xnvi/iot_led/doc/pic/220.jpg

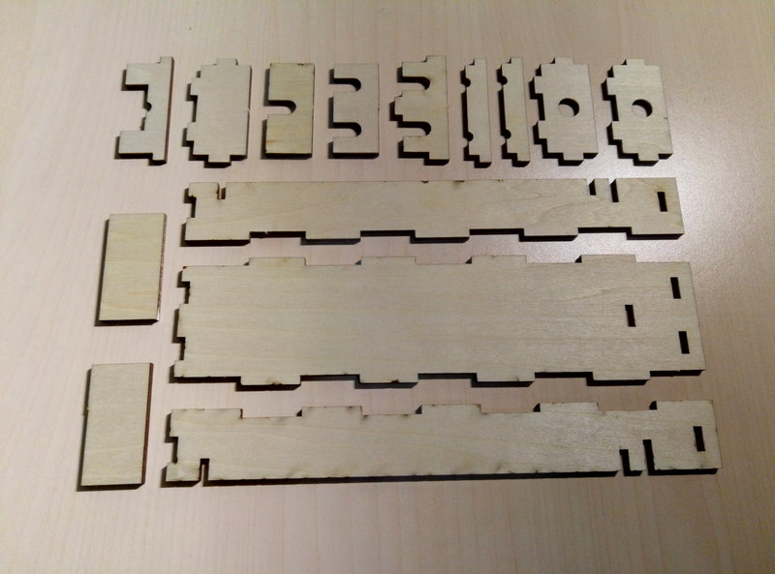
doc/pic/220.jpg
