xnvi/iot_led/doc/pic/260.jpg

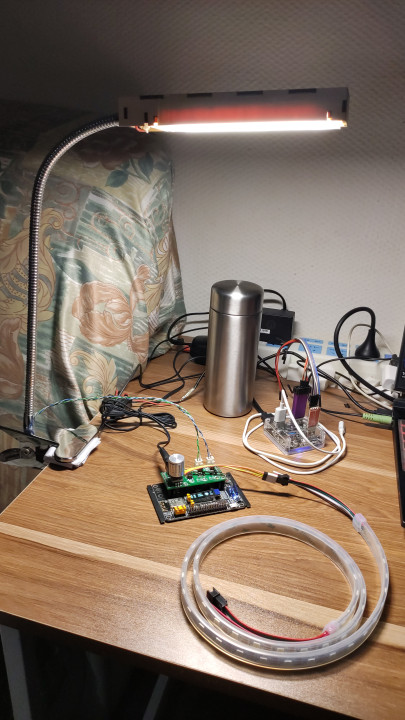
doc/pic/260.jpg
