xnvi/iot_led/doc/原理图及PCB/PCB预览_底面.png

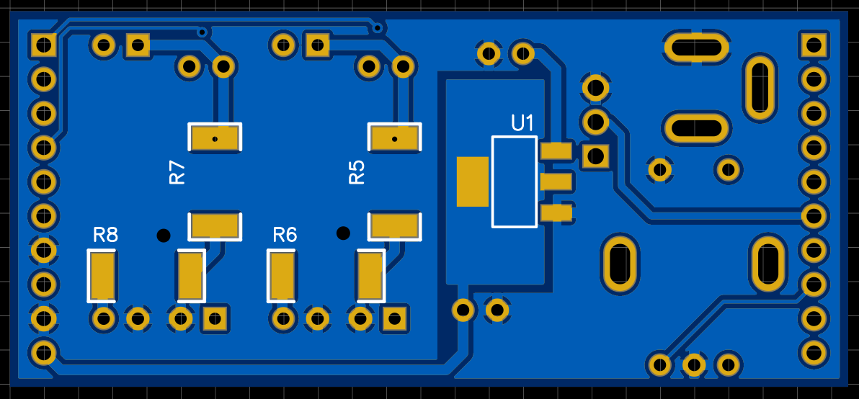
doc/原理图及PCB/PCB预览_底面.png
