xnvi/iot_led/user_code/encoder.h

#ifndef _ENCODER_H
#define _ENCODER_H

// EncoderKeyRet 返回编码器按键状态值
#define ENCODER_KEY_NULL 0x00
#define ENCODER_KEY_RELEASE 0x01
#define ENCODER_KEY_PRESS 0x02

void EncoderInit(void);
void EncoderScan(void);
char ReadEncoder(void);
unsigned char ReadEncoderKey(void);

#endif
