xnvi/iot_led/qcloud-iot-sdk-tencent-at-based/usr_logic/data_template_usr_logic.c

/*
 * Tencent is pleased to support the open source community by making IoT Hub available.
 * Copyright (C) 2019 THL A29 Limited, a Tencent company. All rights reserved.

 * Licensed under the MIT License (the "License"); you may not use this file except in
 * compliance with the License. You may obtain a copy of the License at
 * http://opensource.org/licenses/MIT

 * Unless required by applicable law or agreed to in writing, software distributed under the License is
 * distributed on an "AS IS" basis, WITHOUT WARRANTIES OR CONDITIONS OF ANY KIND,
 * either express or implied. See the License for the specific language governing permissions and
 * limitations under the License.
 *
 */
#include "qcloud_iot_api_export.h"
#include "lite-utils.h"
#include "at_client.h"
#include "string.h"
#include "data_config.c"

#include "user_task.h"


static bool sg_control_msg_arrived = false;
static char sg_data_report_buffer[AT_CMD_MAX_LEN];
static size_t sg_data_report_buffersize = sizeof(sg_data_report_buffer) / sizeof(sg_data_report_buffer[0]);


#ifdef EVENT_POST_ENABLED
#include "events_config.c"
#ifdef	EVENT_TIMESTAMP_USED
static void update_events_timestamp(sEvent *pEvents, int count)
{
	int i;
	
	for(i = 0; i < count; i++){
        if (NULL == (&pEvents[i])) { 
	        Log_e("null event pointer"); 
	        return; 
        }
		pEvents[i].timestamp = HAL_GetTimeSeconds();
	}
}
#endif 

static void event_post_cb(char *msg, void *context)
{
	Log_d("eventReply:%s", msg);
	IOT_Event_clearFlag(context, FLAG_EVENT0|FLAG_EVENT1|FLAG_EVENT2);
}

#endif

#ifdef ACTION_ENABLED
#include "action_config.c"

// action : regist action and set the action handle callback, add your aciton logic here
static void OnActionCallback(void *pClient, const char *pClientToken, DeviceAction *pAction) 
{	
	int i;
	sReplyPara replyPara;

	//do something base on input, just print as an sample
	DeviceProperty *pActionInput = pAction->pInput;
	for (i = 0; i < pAction->input_num; i++) {		
		if (JSTRING == pActionInput[i].type) {
			Log_d("Input:[%s], data:[%s]",  pActionInput[i].key, pActionInput[i].data);
			HAL_Free(pActionInput[i].data);
		} else {
			if(JINT32 == pActionInput[i].type) {
				Log_d("Input:[%s], data:[%d]",  pActionInput[i].key, *((int*)pActionInput[i].data));
			} else if( JFLOAT == pActionInput[i].type) {
				Log_d("Input:[%s], data:[%f]",  pActionInput[i].key, *((float*)pActionInput[i].data));
			} else if( JUINT32 == pActionInput[i].type) {
				Log_d("Input:[%s], data:[%u]",  pActionInput[i].key, *((uint32_t*)pActionInput[i].data));
			}
		}
	}	

	// construct output 
	memset((char *)&replyPara, 0, sizeof(sReplyPara));
	replyPara.code = eDEAL_SUCCESS;
	replyPara.timeout_ms = QCLOUD_IOT_MQTT_COMMAND_TIMEOUT;						
	strcpy(replyPara.status_msg, "action execute success!"); //add the message about the action resault 
	
	
	DeviceProperty *pActionOutnput = pAction->pOutput;	
	(void)pActionOutnput; //elimate warning
	//TO DO: add your aciont logic here and set output properties which will be reported by action_reply
	
	
	IOT_ACTION_REPLY(pClient, pClientToken, sg_data_report_buffer, sg_data_report_buffersize, pAction, &replyPara); 	
}

static int _register_data_template_action(void *pTemplate_client)
{
	int i,rc;
	
    for (i = 0; i < TOTAL_ACTION_COUNTS; i++) {
	    rc = IOT_Template_Register_Action(pTemplate_client, &g_actions[i], OnActionCallback);
	    if (rc != QCLOUD_RET_SUCCESS) {
	        rc = IOT_Template_Destroy(pTemplate_client);
	        Log_e("register device data template action failed, err: %d", rc);
	        return rc;
	    } else {
	        Log_i("data template action=%s registered.", g_actions[i].pActionId);
	    }
    }

	return QCLOUD_RET_SUCCESS;
}
#endif


static void OnControlMsgCallback(void *pClient, const char *pJsonValueBuffer, uint32_t valueLength, DeviceProperty *pProperty) 
{
    int i = 0;

    for (i = 0; i < TOTAL_PROPERTY_COUNT; i++) {		
        if (strcmp(sg_DataTemplate[i].data_property.key, pProperty->key) == 0) {
            sg_DataTemplate[i].state = eCHANGED;
            Log_i("Property=%s changed", pProperty->key);
            sg_control_msg_arrived = true;
            return;
        }
    }

    Log_e("Property=%s changed no match", pProperty->key);
}

/**
 * 注册数据模板属性
 */
static int _register_data_template_property(void *ptemplate_client)
{
	int i,rc;
	
    for (i = 0; i < TOTAL_PROPERTY_COUNT; i++) {
	    rc = IOT_Template_Register_Property(ptemplate_client, &sg_DataTemplate[i].data_property, OnControlMsgCallback);
	    if (rc != QCLOUD_RET_SUCCESS) {
	        rc = IOT_Template_Destroy(ptemplate_client);
	        Log_e("register device data template property failed, err: %d", rc);
	        return rc;
	    } else {
	        Log_i("data template property=%s registered.", sg_DataTemplate[i].data_property.key);
	    }
    }

	return QCLOUD_RET_SUCCESS;
}

static void OnReportReplyCallback(void *pClient, Method method, ReplyAck replyAck, const char *pJsonDocument, void *pUserdata) {
	Log_i("recv report_reply(ack=%d): %s", replyAck,pJsonDocument);
}


/*用户需要实现的下行数据的业务逻辑,待用户实现*/
static void deal_down_stream_user_logic(void *pClient, ProductDataDefine * pData)
{
	// Log_d("someting about your own product logic wait to be done");

	set_brightness(pData->m_brightness);
	set_color_temp(pData->m_color_temp);
	power_switch(pData->m_power_switch);
	set_colorful_mode(pData->m_colorful_mode, pData->m_default_color_mode,
	                  (pData->m_red << 16) + (pData->m_green << 8) + (pData->m_blue));
}

/*用户需要实现的上行数据的业务逻辑,此处仅供示例*/
static int deal_up_stream_user_logic(void *pClient, DeviceProperty *pReportDataList[], int *pCount)
{
	int i, j;
	
	//check local property state
	//_refresh_local_property. if property changed, set sg_DataTemplate[i].state = eCHANGED;
	
    for (i = 0, j = 0; i < TOTAL_PROPERTY_COUNT; i++) {       
        if(eCHANGED == sg_DataTemplate[i].state) {
            pReportDataList[j++] = &(sg_DataTemplate[i].data_property);
			sg_DataTemplate[i].state = eNOCHANGE;
        }
    }
	*pCount = j;

	return (*pCount > 0)?QCLOUD_RET_SUCCESS:QCLOUD_ERR_FAILURE;
}

static eAtResault net_prepare(void)
{
	eAtResault Ret;
	DeviceInfo sDevInfo;
	at_client_t pclient = at_client_get();	

	memset((char *)&sDevInfo, '\0', sizeof(DeviceInfo));
	Ret = (eAtResault)HAL_GetDevInfo(&sDevInfo);
	if(QCLOUD_RET_SUCCESS != Ret){
		Log_e("Get device info err");
		return QCLOUD_ERR_FAILURE;
	}
	
	if(QCLOUD_RET_SUCCESS != module_init(eMODULE_ESP8266)) 
	{
		Log_e("module init failed");
		goto exit;
	}
	else
	{
		Log_d("module init success");	
	}

	//wait at parse thread run
	while(AT_STATUS_INITIALIZED != pclient->status)
	{	
		HAL_SleepMs(1000);
	}
	
	Log_d("Start shakehands with module...");
	Ret = module_handshake(CMD_TIMEOUT_MS);
	if(QCLOUD_RET_SUCCESS != Ret)
	{
		Log_e("module connect fail,Ret:%d", Ret);
		goto exit;
	}
	else
	{
		Log_d("module connect success");
	}
	
	Ret = iot_device_info_init(sDevInfo.product_id, sDevInfo.device_name, sDevInfo.devSerc);
	if(QCLOUD_RET_SUCCESS != Ret)
	{
		Log_e("dev info init fail,Ret:%d", Ret);
		goto exit;
	}

	Ret = module_info_set(iot_device_info_get(), ePSK_TLS);
	if(QCLOUD_RET_SUCCESS != Ret)
	{
		Log_e("module info set fail,Ret:%d", Ret);
	}

exit:

	return Ret;
}

static void eventPostCheck(void *client)
{
#ifdef EVENT_POST_ENABLED	
	int rc;
	int i;
	uint32_t eflag;
	sEvent *pEventList[EVENT_COUNTS];
	uint8_t event_count;
		
	//事件上报
	IOT_Event_setFlag(client, FLAG_EVENT0|FLAG_EVENT1|FLAG_EVENT2);
	eflag = IOT_Event_getFlag(client);
	if((EVENT_COUNTS > 0 )&& (eflag > 0))
	{	
		event_count = 0;
		for(i = 0; i < EVENT_COUNTS; i++)
		{
		
			if((eflag&(1<<i))&ALL_EVENTS_MASK)
			{
				 pEventList[event_count++] = &(g_events[i]);				 
				 IOT_Event_clearFlag(client, 1<<i);
#ifdef	EVENT_TIMESTAMP_USED				 
				 update_events_timestamp(&g_events[i], 1);
#endif
			}			
		}	

		rc = IOT_Post_Event(client, sg_data_report_buffer, sg_data_report_buffersize, \
											event_count, pEventList, event_post_cb);
		if(rc < 0)
		{
			Log_e("events post failed: %d", rc);
		}
	}
#endif

}

/*用户需要实现设备信息获取,此处示例实现*/
static int _get_sys_info(void *handle, char *pJsonDoc, size_t sizeOfBuffer)
{
	/*平台处理字段，必选字段至少有一个*/
    DeviceProperty plat_info[] = {
     	{.key = "module_hardinfo", .type = TYPE_TEMPLATE_STRING, .data = "ESP8266"},
     	{.key = "module_softinfo", .type = TYPE_TEMPLATE_STRING, .data = "V1.0"},
     	{.key = "fw_ver", 		   .type = TYPE_TEMPLATE_STRING, .data = QCLOUD_IOT_AT_SDK_VERSION},
     	// {.key = "imei", 		   .type = TYPE_TEMPLATE_STRING, .data = "11-22-33-44"},
     	// {.key = "lat", 			   .type = TYPE_TEMPLATE_STRING, .data = "22.546015"},
     	// {.key = "lon", 			   .type = TYPE_TEMPLATE_STRING, .data = "113.941125"},
        {NULL, NULL, JINT32}  //结束
	};
		
	/*自定义附加信息*/
	DeviceProperty self_info[] = {
        {.key = "append_info", .type = TYPE_TEMPLATE_STRING, .data = "your self define ifno"},
        {NULL, NULL, JINT32}  //结束
	};

	return IOT_Template_JSON_ConstructSysInfo(handle, pJsonDoc, sizeOfBuffer, plat_info, self_info); 	
}


void data_template_demo_task(void *arg)
{
	eAtResault Ret;
	int rc;
	int ReportCont;
	void *client = NULL;
	at_client_t pclient = at_client_get();	
	DeviceProperty *pReportDataList[TOTAL_PROPERTY_COUNT];

	Log_d("data_template_demo_task Entry...");
	do  
	{
		Ret = net_prepare();
		if(QCLOUD_RET_SUCCESS != Ret)
		{
			Log_e("net prepare fail,Ret:%d", Ret);
			break;
		}

		/*
		 *注意：module_register_network 联网需要根据所选模组适配修改实现
		*/
		Ret = module_register_network(eMODULE_ESP8266);
		if(QCLOUD_RET_SUCCESS != Ret)
		{			
			Log_e("network connect fail,Ret:%d", Ret);
			break;
		}

		
		MQTTInitParams init_params = DEFAULT_MQTTINIT_PARAMS;
		Ret = module_mqtt_conn(init_params);
		if(QCLOUD_RET_SUCCESS != Ret)
		{
			Log_e("module mqtt conn fail,Ret:%d", Ret);
			break;
		}
		else
		{
			Log_d("module mqtt conn success");
		}

		
		if(!IOT_MQTT_IsConnected())
		{
			Log_e("mqtt connect fail");
			break;
		}

		Ret = (eAtResault)IOT_Template_Construct(&client);
		if(QCLOUD_RET_SUCCESS != Ret)
		{
			Log_e("data template construct fail,Ret:%d", Ret);
			break;
		}
		else
		{
			Log_d("data template construct success");
		}

		//init data template
		_init_data_template();

				
		//register data template propertys here
		rc = _register_data_template_property(client);
		if (rc == QCLOUD_RET_SUCCESS) 
		{
			Log_i("Register data template propertys Success");
		} 
		else 
		{
			Log_e("Register data template propertys Failed: %d", rc);
			break;
		}

#ifdef ACTION_ENABLED
		//register data template actions
		rc = _register_data_template_action(client);
		if (rc == QCLOUD_RET_SUCCESS) {
			Log_i("Register data template actions Success");
		} else {
			Log_e("Register data template actions Failed: %d", rc);
			break;
		}
#endif
			
		//上报设备信息,平台根据这个信息提供产品层面的数据分析,譬如位置服务等
		rc = _get_sys_info(client, sg_data_report_buffer, sg_data_report_buffersize);
		if(QCLOUD_RET_SUCCESS == rc)
		{
			rc = IOT_Template_Report_SysInfo_Sync(client, sg_data_report_buffer, sg_data_report_buffersize, QCLOUD_IOT_MQTT_COMMAND_TIMEOUT);	
			if (rc != QCLOUD_RET_SUCCESS) 
			{
				Log_e("Report system info fail, err: %d", rc);
				break;
			}
		}
		else
		{
			Log_e("Get system info fail, err: %d", rc);
			break;
		}

		//获取离线期间数据
		rc = IOT_Template_GetStatus_sync(client, QCLOUD_IOT_MQTT_COMMAND_TIMEOUT);
		if (rc != QCLOUD_RET_SUCCESS) 
		{
			Log_e("Get data status fail, err: %d", rc);
			break;
		}
		else
		{
			Log_d("Get data status success");
		}


		while(1)
		{
			HAL_SleepMs(1000);
			IOT_Template_Yield(client, 2000);
			
			/*服务端下行消息，业务处理逻辑1入口*/
			if (sg_control_msg_arrived) {	
				
				deal_down_stream_user_logic(client, &sg_ProductData);				
				//业务逻辑处理完后需要通知服务端control msg 已收到，请服务端删除control msg，否则服务端会保留control msg(通过Get status命令可以得到未删除的Control数据)
				sReplyPara replyPara;
				memset((char *)&replyPara, 0, sizeof(sReplyPara));
				replyPara.code = eDEAL_SUCCESS;
				replyPara.timeout_ms = QCLOUD_IOT_MQTT_COMMAND_TIMEOUT;						
				replyPara.status_msg[0] = '\0';			//可以通过 replyPara.status_msg 添加附加消息，一般在失败情况下才添加
				
				rc = IOT_Template_ControlReply(client, sg_data_report_buffer, sg_data_report_buffersize, &replyPara);
	            if (rc == QCLOUD_RET_SUCCESS) {
					Log_d("Contol msg reply success");
					sg_control_msg_arrived = false;   
	            } else {
	                Log_e("Contol msg reply failed, err: %d", rc);
					break;
	            }				
			}	

			/*设备上行消息,业务逻辑2入口*/								
			if(QCLOUD_RET_SUCCESS == deal_up_stream_user_logic(client, pReportDataList, &ReportCont)){
				
				rc = IOT_Template_JSON_ConstructReportArray(client, sg_data_report_buffer, sg_data_report_buffersize, ReportCont, pReportDataList);
				if (rc == QCLOUD_RET_SUCCESS) {
					rc = IOT_Template_Report(client, sg_data_report_buffer, sg_data_report_buffersize, 
												OnReportReplyCallback, NULL, QCLOUD_IOT_MQTT_COMMAND_TIMEOUT);
					if (rc == QCLOUD_RET_SUCCESS) {
						Log_d("data template reporte success");
					} else {
						Log_e("data template reporte failed, err: %d", rc);
						break;
					}
				} else {
					Log_e("construct reporte data failed, err: %d", rc);
					break;
				}
		
			}
			
			// TODO 暂时不需要上报事件，以后要用再开发
			// eventPostCheck(client);
		}				
	}while (0);
	
	hal_thread_destroy(NULL);
	Log_e("Task teminated,Something goes wrong!!!");
}

void data_template_sample(void)
{
	osThreadId demo_threadId;
	
#ifdef OS_USED
	// TODO 默认512，改大一点，实际测试需要3K，根据自己实际情况修改
	hal_thread_create(&demo_threadId, 3072, osPriorityNormal, data_template_demo_task, NULL);
	hal_thread_destroy(NULL);
#else
	#error os should be used just now
#endif
}

extern void start_user_task(void *arg);

void application_entry(void *arg)
{
	start_user_task(NULL);
	data_template_sample();
}
