xnvi/iot_led/user_code/ascii12.h

#ifndef _ASCII12_H
#define _ASCII12_H

//��λ��ǰȡģ
/*
const unsigned char ASCII12 [1140] = {
0x00,0x00,0x00,0x00,0x00,0x00,0x00,0x00,0x00,0x00,0x00,0x00,
0x00,0x00,0x7F,0x00,0x00,0x00,0x00,0x00,0xA0,0x00,0x00,0x00,
0x00,0x60,0x00,0x60,0x00,0x00,0x00,0x00,0x00,0x00,0x00,0x00,
0x11,0x7F,0x11,0x7F,0x11,0x00,0x00,0xE0,0x00,0xE0,0x00,0x00,
0x18,0x24,0x7F,0x22,0x11,0x00,0x80,0x40,0xE0,0x40,0x80,0x00,
0x30,0x49,0x36,0x19,0x60,0x00,0x60,0x80,0xC0,0x20,0xC0,0x00,
0x3B,0x44,0x46,0x39,0x02,0x00,0xC0,0x20,0x20,0xC0,0x20,0x00,
0x00,0x00,0x60,0x00,0x00,0x00,0x00,0x00,0x00,0x00,0x00,0x00,
0x00,0x0F,0x30,0x40,0x00,0x00,0x00,0x00,0xC0,0x20,0x00,0x00,
0x00,0x40,0x30,0x0F,0x00,0x00,0x00,0x20,0xC0,0x00,0x00,0x00,
0x11,0x0A,0x3F,0x0A,0x11,0x00,0x00,0x00,0x80,0x00,0x00,0x00,
0x04,0x04,0x1F,0x04,0x04,0x00,0x00,0x00,0x00,0x00,0x00,0x00,
0x00,0x00,0x00,0x00,0x00,0x00,0x00,0xA0,0xC0,0x00,0x00,0x00,
0x04,0x04,0x04,0x04,0x04,0x00,0x00,0x00,0x00,0x00,0x00,0x00,
0x00,0x00,0x00,0x00,0x00,0x00,0x00,0x60,0x60,0x00,0x00,0x00,
0x00,0x01,0x06,0x18,0x60,0x00,0x60,0x80,0x00,0x00,0x00,0x00,
0x3F,0x41,0x42,0x44,0x3F,0x00,0xC0,0x20,0x20,0x20,0xC0,0x00,
0x00,0x20,0x7F,0x00,0x00,0x00,0x00,0x20,0xE0,0x20,0x00,0x00,
0x30,0x41,0x42,0x44,0x38,0x00,0xE0,0x20,0x20,0x20,0x20,0x00,
0x30,0x40,0x44,0x44,0x3B,0x00,0xC0,0x20,0x20,0x20,0xC0,0x00,
0x03,0x0C,0x30,0x7F,0x00,0x00,0x80,0x80,0x80,0xE0,0x80,0x00,
0x7C,0x44,0x44,0x44,0x43,0x00,0x40,0x20,0x20,0x20,0xC0,0x00,
0x3F,0x44,0x44,0x44,0x23,0x00,0xC0,0x20,0x20,0x20,0xC0,0x00,
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
0xfe,0x02,0x02,0x02,0xfc,0x00,0x07,0x04,0x04,0x04,0x03,0x00,
0xfe,0x22,0x22,0x22,0x02,0x00,0x07,0x04,0x04,0x04,0x04,0x00,
0xfe,0x22,0x22,0x22,0x02,0x00,0x07,0x00,0x00,0x00,0x00,0x00,
0xfc,0x02,0x42,0x42,0xcc,0x00,0x03,0x04,0x04,0x02,0x07,0x00,
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
};

#endif
