xnvi/iot_led/user_code/zh_cn12.h

/*
字库取模方式
目前用的 PCtoLCD2002
阴码 逆向（低位在前） 列行式

*/


#ifndef _ZH_CN12_H
#define _ZH_CN12_H

// #include "myinteger.h"
#include<stdint.h>

// 使用用户字库，或使用默认字库，默认字库为字频表前1024字，可覆盖大部分使用场景
#define USE_USER_FONT_TABLE 1
#define USE_DEFAULT_FONT_TABLE 0


typedef struct _FONT12_STRUCT
{
	uint8_t character[3];
	uint8_t reserve;
	uint8_t fontdata[24];
}font12_struct;


#if 0
// !!!! 二分查找要求所有汉字索引必须排序 !!!!
// const font12_struct font12_table[] = 
const font12_struct font12_table[] = 
{
	{"测", 0, {0x22,0x44,0xFE,0x02,0xFA,0x02,0xFE,0x00,0xFC,0x00,0xFF,0x00,0x04,0x02,0x09,0x04,0x03,0x04,0x09,0x00,0x01,0x08,0x0F,0x00},},
	{"试", 0, {0x11,0xF2,0x00,0x00,0x24,0xE4,0x24,0x04,0xFF,0x04,0x05,0x00,0x00,0x0F,0x04,0x00,0x04,0x07,0x02,0x00,0x03,0x04,0x0E,0x00},},
	{"文", 0, {0x04,0x04,0x1C,0x64,0x85,0x06,0x84,0x64,0x1C,0x04,0x04,0x00,0x08,0x08,0x04,0x04,0x02,0x01,0x02,0x04,0x04,0x08,0x08,0x00},},
	{"中", 0, {0x00,0xF8,0x88,0x88,0x88,0xFF,0x88,0x88,0x88,0xF8,0x00,0x00,0x00,0x01,0x00,0x00,0x00,0x0F,0x00,0x00,0x00,0x01,0x00,0x00},},
};
#endif


#if USE_USER_FONT_TABLE

const font12_struct font12_table[] = 
{
	{"亮", 0, {0x82,0x82,0xBA,0xAA,0xAA,0xAB,0xAA,0xAA,0xBA,0x82,0x82,0x00,0x09,0x08,0x06,0x02,0x02,0x02,0x02,0x06,0x08,0x08,0x0D,0x00},},
	{"度", 0, {0x00,0xFE,0x0A,0x8A,0xBE,0xAA,0xAB,0xAA,0xBE,0x8A,0x0A,0x00,0x08,0x07,0x00,0x08,0x09,0x0A,0x04,0x04,0x0A,0x09,0x08,0x00},},
	{"色", 0, {0x08,0xF4,0x92,0x93,0x92,0xF2,0x92,0x9A,0x96,0xF0,0x00,0x00,0x00,0x07,0x08,0x08,0x08,0x08,0x08,0x08,0x08,0x08,0x0E,0x00},},
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
	{"九", 0, {0x08,0x08,0x08,0xFF,0x08,0x08,0x08,0xF8,0x00,0x00,0x00,0x00,0x08,0x04,0x03,0x00,0x00,0x00,0x00,0x07,0x08,0x08,0x0E,0x00},},
	{"十", 0, {0x20,0x20,0x20,0x20,0x20,0xFF,0x20,0x20,0x20,0x20,0x20,0x00,0x00,0x00,0x00,0x00,0x00,0x0F,0x00,0x00,0x00,0x00,0x00,0x00},},
	{"，", 0, {0x00,0x00,0xC0,0xC0,0x00,0x00,0x00,0x00,0x00,0x00,0x00,0x00,0x00,0x00,0x02,0x01,0x00,0x00,0x00,0x00,0x00,0x00,0x00,0x00},},
	{"。", 0, {0x00,0x00,0xC0,0x20,0x20,0xC0,0x00,0x00,0x00,0x00,0x00,0x00,0x00,0x00,0x00,0x01,0x01,0x00,0x00,0x00,0x00,0x00,0x00,0x00},},
};

#endif // USE_USER_FONT_TABLE



#if USE_DEFAULT_FONT_TABLE

const font12_struct font12_table[] = 
{

};

#endif // USE_USER_FONT_TABLE

#endif // _ZH_CN12_H
