xnvi/iot_led/qcloud-iot-sdk-tencent-at-based/port/hal_os.c

/*
 * Tencent is pleased to support the open source community by making IoT Hub available.
 * Copyright (C) 2016 THL A29 Limited, a Tencent company. All rights reserved.

 * Licensed under the MIT License (the "License"); you may not use this file except in
 * compliance with the License. You may obtain a copy of the License at
 * http://opensource.org/licenses/MIT

 * Unless required by applicable law or agreed to in writing, software distributed under the License is
 * distributed on an "AS IS" basis, WITHOUT WARRANTIES OR CONDITIONS OF ANY KIND,
 * either express or implied. See the License for the specific language governing permissions and
 * limitations under the License.
 *
 */

#include <stdio.h>
#include <stdlib.h>
#include <stdarg.h>
#include <string.h>
#include "stm32g0xx_hal.h"		
#include "qcloud_iot_api_export.h"
#include "tos_k.h"
#include "user_config.h"

#ifdef  DEBUG_DEV_INFO_USED

/* 产品名称, 与云端同步设备状态时需要  */
static char sg_product_id[MAX_SIZE_OF_PRODUCT_ID + 1]	 = USER_PRODUCT_ID;
/* 设备名称, 与云端同步设备状态时需要 */
static char sg_device_name[MAX_SIZE_OF_DEVICE_NAME + 1]  = USER_DEVICE_NAME;

#ifdef DEV_DYN_REG_ENABLED
/* 产品密钥, 若使能动态注册功能，控制台生成，必填。若不使能，则不用赋值  */
static char sg_product_secret[MAX_SIZE_OF_PRODUCT_SECRET + 1]  = "YOUR_PRODUCT_SECRET";
#endif

#ifdef AUTH_MODE_CERT
/* 客户端证书文件名  非对称加密使用, TLS 证书认证方式*/
static char sg_device_cert_file_name[MAX_SIZE_OF_DEVICE_CERT_FILE_NAME + 1]      = "YOUR_DEVICE_NAME_cert.crt";
/* 客户端私钥文件名 非对称加密使用, TLS 证书认证方式*/
static char sg_device_privatekey_file_name[MAX_SIZE_OF_DEVICE_KEY_FILE_NAME + 1] = "YOUR_DEVICE_NAME_private.key";
#else
/* 设备密钥, TLS PSK认证方式*/
static char sg_device_secret[MAX_SIZE_OF_DEVICE_SERC + 1] = USER_DEVICE_SECRET;
#endif


#endif

void HAL_Printf(_IN_ const char *fmt, ...)
{
    va_list args;

    va_start(args, fmt);
    vprintf(fmt, args);
    va_end(args);

    fflush(stdout);
}

int HAL_Snprintf(_IN_ char *str, const int len, const char *fmt, ...)
{
    va_list args;
    int rc;

    va_start(args, fmt);
    rc = vsnprintf(str, len, fmt, args);
    va_end(args);

    return rc;
}

int HAL_Vsnprintf(_IN_ char *str, _IN_ const int len, _IN_ const char *format, va_list ap)
{
    return vsnprintf(str, len, format, ap);
}


void HAL_DelayUs(_IN_ uint32_t us)
{
    HAL_Delay(us);
}

uint32_t HAL_GetTimeMs(void)
{	
    return HAL_GetTick();
}

uint32_t HAL_GetTimeSeconds(void)
{	
    return HAL_GetTimeMs()/1000;
}


void HAL_DelayMs(_IN_ uint32_t ms)
{
   (void)HAL_Delay(ms);
}

#ifdef OS_USED

// 实际使用中AT SDK一共创建2个任务
#define AT_SDK_TASK_NUM 2
#define AT_SDK_TASK_NAME_LEN 16

char task_name_list[AT_SDK_TASK_NUM][AT_SDK_TASK_NAME_LEN];
k_task_t *task_list[AT_SDK_TASK_NUM];
	
void hal_thread_create(volatile void* threadId, uint16_t stackSize, int Priority, void (*fn)(void*), void* arg)
{
	int i = 0;
	k_err_t err;

	for(i=0; i<AT_SDK_TASK_NUM; i++)
	{
		if(task_list[i] == NULL)
		{
			break;
		}
	}

	sprintf(&task_name_list[i][0], "at_task_%d", i);

	err = tos_task_create_dyn((k_task_t **)threadId,
							  &task_name_list[i][0],
							  (k_task_entry_t)fn,
							  arg,
							  4,
							  stackSize,
							  0);
	if (err != K_ERR_NONE)
	{
		printf("hal_thread_create err, ret %d\n", err);
	}
	task_list[i] = (k_task_t *)threadId;
}

void hal_thread_destroy(void* threadId)
{
	k_err_t err;
	int i = 0;

	for(i=0; i<AT_SDK_TASK_NUM; i++)
	{
		if(task_list[i] == threadId)
		{
			task_list[i] = NULL;
			memset(&task_name_list[i][0], 0, AT_SDK_TASK_NAME_LEN);
			break;
		}
	}

	err = tos_task_destroy(threadId);
	if (err != K_ERR_NONE)
	{
		printf("hal_thread_destroy err, ret %d\n", err);
	}
}

void HAL_SleepMs(_IN_ uint32_t ms)
{
   (void)osDelay(ms);
}

void *HAL_Malloc(_IN_ uint32_t size)
{
	return tos_mmheap_alloc(size);
}

void HAL_Free(_IN_ void *ptr)
{
	tos_mmheap_free(ptr);
}


// 锁的数量请根据实际情况修改
#define LOCK_NUM 4
k_mutex_t lock_list[LOCK_NUM];
unsigned char lock_index[LOCK_NUM] = {0};

void *HAL_MutexCreate(void)
{
	k_err_t err;
	int i = 0;
	for(i=0; i<LOCK_NUM; i++)
	{
		if(lock_index[i] == 0)
		{
			lock_index[i] = 1;
			break;
		}
	}

	if(i >= LOCK_NUM)
	{
		return NULL;
	}
	
	err = tos_mutex_create(&lock_list[i]);
    return err == K_ERR_NONE ? &lock_list[i] : NULL;
}


void HAL_MutexDestroy(_IN_ void * mutex)
{
	int i = 0;
	for(i=0; i<LOCK_NUM; i++)
	{
		if(&lock_list[i] == mutex)
		{
			lock_index[i] = 0;
			break;
		}
	}

	tos_mutex_destroy((k_mutex_t *)mutex);
}

void HAL_MutexLock(_IN_ void * mutex)
{
	k_err_t ret;
	ret = tos_mutex_pend_timed((k_mutex_t *)mutex, TOS_TIME_FOREVER);
	if(ret)
	{
		HAL_Printf("HAL_MutexLock err, err:%d\n\r",ret);
	}
}

void HAL_MutexUnlock(_IN_ void * mutex)
{
	k_err_t ret;
	ret = tos_mutex_post((k_mutex_t *)mutex);
	if(ret)
	{
		HAL_Printf("HAL_MutexUnlock err, err:%d\n\r",ret);
	}	
}
#else
void hal_thread_create(void** threadId, void (*fn)(void*), void* arg)
{

}

void HAL_SleepMs(_IN_ uint32_t ms)
{
	(void)HAL_Delay(ms);
}

void *HAL_Malloc(_IN_ uint32_t size)
{
	return malloc(size);
}

void HAL_Free(_IN_ void *ptr)
{
   free(ptr);
}

void *HAL_MutexCreate(void)
{
	return (void *)1;
}


void HAL_MutexDestroy(_IN_ void* mutex)
{
	return;
}

void HAL_MutexLock(_IN_ void* mutex)
{
	return;
}

void HAL_MutexUnlock(_IN_ void* mutex)
{
	return;
}

#endif

int HAL_SetDevInfo(void *pdevInfo)
{
	int ret = QCLOUD_RET_SUCCESS;;
	DeviceInfo *devInfo = (DeviceInfo *)pdevInfo;
	

	if(NULL == pdevInfo){
		return QCLOUD_ERR_FAILURE;
	}
	
#ifdef DEBUG_DEV_INFO_USED
	memset(sg_product_id, '\0', MAX_SIZE_OF_PRODUCT_ID);	
	memset(sg_device_name, '\0', MAX_SIZE_OF_DEVICE_NAME);
	
	strncpy(sg_product_id, devInfo->product_id, MAX_SIZE_OF_PRODUCT_ID);
	strncpy(sg_device_name, devInfo->device_name, MAX_SIZE_OF_DEVICE_NAME);
	
#ifdef DEV_DYN_REG_ENABLED
	memset(sg_product_secret, '\0', MAX_SIZE_OF_PRODUCT_SECRET);
	strncpy(sg_product_secret, devInfo->product_secret, MAX_SIZE_OF_PRODUCT_KEY);
#endif
	
#ifdef 	AUTH_MODE_CERT
	memset(sg_device_cert_file_name, '\0', MAX_SIZE_OF_DEVICE_CERT_FILE_NAME);
	memset(sg_device_privatekey_file_name, '\0', MAX_SIZE_OF_DEVICE_KEY_FILE_NAME);
	
	strncpy(sg_device_cert_file_name, devInfo->devCertFileName, MAX_SIZE_OF_DEVICE_CERT_FILE_NAME);
	strncpy(sg_device_privatekey_file_name, devInfo->devPrivateKeyFileName, MAX_SIZE_OF_DEVICE_KEY_FILE_NAME);
#else
	memset(sg_device_secret, '\0', MAX_SIZE_OF_DEVICE_SERC);
	strncpy(sg_device_secret, devInfo->devSerc, MAX_SIZE_OF_DEVICE_SERC);
#endif
		
#else
	 Log_e("HAL_SetDevInfo is not implement");
	 (void)devInfo; //eliminate compile warning

	 return QCLOUD_ERR_FAILURE;

#endif

	return ret;
}

int HAL_GetDevInfo(void *pdevInfo)
{
	int ret = QCLOUD_RET_SUCCESS;
	DeviceInfo *devInfo = (DeviceInfo *)pdevInfo;

	if(NULL == pdevInfo){
		return QCLOUD_ERR_FAILURE;
	}
	
	memset((char *)devInfo, '\0', sizeof(DeviceInfo));	
	
#ifdef DEBUG_DEV_INFO_USED	

	strncpy(devInfo->product_id, sg_product_id, MAX_SIZE_OF_PRODUCT_ID);
	strncpy(devInfo->device_name, sg_device_name, MAX_SIZE_OF_DEVICE_NAME);
	
#ifdef DEV_DYN_REG_ENABLED
	memset(devInfo->product_secret, '\0', MAX_SIZE_OF_PRODUCT_SECRET);
	strncpy(devInfo->product_secret, sg_product_secret, MAX_SIZE_OF_PRODUCT_SECRET);
#endif	
	
#ifdef 	AUTH_MODE_CERT
	strncpy(devInfo->devCertFileName, sg_device_cert_file_name, MAX_SIZE_OF_DEVICE_CERT_FILE_NAME);
	strncpy(devInfo->devPrivateKeyFileName, sg_device_privatekey_file_name, MAX_SIZE_OF_DEVICE_KEY_FILE_NAME);
#else
	strncpy(devInfo->devSerc, sg_device_secret, MAX_SIZE_OF_DEVICE_SERC);
#endif 

#else
   Log_e("HAL_GetDevInfo is not implement");

   return QCLOUD_ERR_FAILURE;
#endif

	return ret;
}
