xnvi/iot_led/user_code/user_config.h

#ifndef __USER_CONFIG_H
#define __USER_CONFIG_H

// 这里填入你自己的信息
#define USER_PRODUCT_ID    "10字节产品ID"
#define USER_DEVICE_NAME   "不超过48字节的设备名"
#define USER_DEVICE_SECRET "24字节的设备密钥"
#define USER_WIFI_SSID     "你的WIFI名"
#define USER_WIFI_PW       "你的WIFI密码"

#endif
