xnvi/iot_led/user_code/user_task.h

#ifndef __USER_TASK_H
#define __USER_TASK_H

#include <stdint.h>

// void start_user_task(void *arg);

void set_colorful_mode(uint8_t mode, uint32_t default_color_mode, uint32_t color);
void power_switch(int32_t sw);
void set_brightness(int32_t brightness);
void set_color_temp(int32_t k);

#endif
